rodeo-sam/SolderingIron/Hardware/Emergy-Stop_Spice/Emergency_Stop.asc

C2: cap; 1µ
D2: diode; 1N4148
M1: nmos; BSS123
M2: pmos; irf7424
M3: nmos; BSS123
R1: res; 430k
R2: res; 1k
R3: res; 6.2k
R4: res; 11k
R5: res; 200k
R6: res; 100k
R8: res; 330k
R9: res; 1k
R10: res; 68k
R11: res; 100k
R12: res; 20k
R13: res; 100k
R14: res; 220k
R15: res; 100
R16: res; 100
R36: res; 10k
R37: res; 10k
R_heater: res; 3
R_wire: res; 0.01
U1: opamp2; LM324
U3: opamp2; LM324
U4: opamp2; LM324
U5: opamp2; LM324
V_thermo: voltage; PULSE({T} 0.010230859 2 0 0 4)
Vcc: voltage; 5
Vpwm: voltage; PULSE(0 5 0 0 0 0.001 0.1)
Vsupply: voltage; 12
Named nets: 0, +5V, heater, +12V, pwm, safety, sensor, thermo_raw, thermo_coarse, thermo_voltage, thermo_coarse_inv
.inc parts/LM324.5_1
.inc parts/BSS123.prm
.inc parts/irf7424.spi
.tran 0 10 0
.step param P list 0.0 0.01 0.05 0.09 0.095 0.0999
.step param T 0.000699451 0.010230859 0.000953141
.inc parts/ts914_spice.txt
.step param P list 0.0 0.001 0.090 0.099 0.0999
