rodeo-sam/SolderingIron/Firmware_v1/includes/temperature.h

/*
 * temperature.h
 *
 * Created: Fr 30. Jan 15:43:17 CET 2015
 * Author: Karsten Hinz <k.hinz tu-bs.de>
 */ 

#pragma once

int8_t measure_get_internal_temperature();
int16_t measure_get_soldertip_temperature();
