rodeo-sam/SolderingIron/Firmware_v1/tests/test_tip_temp.c

/*
 * test_tip_temp.c 
 *
 * Created: Mi 4. Feb 16:53:09 CET 2015
 * Author: Karsten Hinz <k.hinz@tu-bs.de>
 */ 

#include <util/delay.h>
#include "display.h"
#include "config.h"
#include <stdio.h>
#include "uart.h"
#include "adc.h"
#include "temperature.h"
#include "tip.h"
#include <avr/interrupt.h>

void show_temperature(int16_t temp) {
	display_temperature(temp);
	printf("%i\r\n", temp);
}

int main(void)
{
	uart_init(19200, one_stop_bit_e, no_parity_e);
	display_init();
	tip_init(&show_temperature);

	display_digit(1,4);

	sei();
	printf_P(PSTR("\r\nSolder Tip Temperature test\r\n "));

	tip_startConversion();


	while(1)
	{
		display_update();
		_delay_ms(2);
	}
}
